ewan-ginger/radian_/Code/Firmware/Waveshare ESP32-S3-LCD-1.85/Arduino/examples/Master/LVGL_Driver.cpp

/*****************************************************************************
  | File        :   LVGL_Driver.c
  
  | help        : 
    The provided LVGL library file must be installed first
******************************************************************************/
#include "LVGL_Driver.h"

static lv_disp_draw_buf_t draw_buf;
static lv_color_t buf1[ LVGL_BUF_LEN ];
static lv_color_t buf2[ LVGL_BUF_LEN];
// static lv_color_t* buf1 = (lv_color_t*) heap_caps_malloc(LVGL_BUF_LEN , MALLOC_CAP_SPIRAM);
// static lv_color_t* buf2 = (lv_color_t*) heap_caps_malloc(LVGL_BUF_LEN , MALLOC_CAP_SPIRAM);
    
/*  Display flushing 
    Displays LVGL content on the LCD
    This function implements associating LVGL data to the LCD screen
*/
void Lvgl_Display_LCD( lv_disp_drv_t *disp_drv, const lv_area_t *area, lv_color_t *color_p )
{
  LCD_addWindow(area->x1, area->y1, area->x2, area->y2, ( uint16_t *)&color_p->full);
  lv_disp_flush_ready( disp_drv );
}
/*Read the touchpad*/
void Lvgl_Touchpad_Read( lv_indev_drv_t * indev_drv, lv_indev_data_t * data )
{
  Simulated_Touch();
  if (touch_data.points != 0x00) {
    data->point.x = touch_data.x;
    data->point.y = touch_data.y;
    data->state = LV_INDEV_STATE_PR;
    // printf("LVGL : X=%u Y=%u points=%d\r\n",  touch_data.x , touch_data.y,touch_data.points);
  } else {
    data->state = LV_INDEV_STATE_REL;
  }
  touch_data.x = 0;
  touch_data.y = 0;
  touch_data.points = 0;
}
void example_increase_lvgl_tick(void *arg)
{
    /* Tell LVGL how many milliseconds has elapsed */
    lv_tick_inc(EXAMPLE_LVGL_TICK_PERIOD_MS);
}
void example_increase_lvgl_Loop_tick(void *arg)
{
  lv_timer_handler(); /* let the GUI do its work */
}
void Lvgl_Init(void)
{
  lv_init();
  lv_disp_draw_buf_init( &draw_buf, buf1, buf2, LVGL_BUF_LEN);

  /*Initialize the display*/
  static lv_disp_drv_t disp_drv;
  lv_disp_drv_init( &disp_drv );
  /*Change the following line to your display resolution*/
  disp_drv.hor_res = LCD_WIDTH;
  disp_drv.ver_res = LCD_HEIGHT;
  disp_drv.flush_cb = Lvgl_Display_LCD;
  disp_drv.full_refresh = 1;                    /**< 1: Always make the whole screen redrawn*/
  disp_drv.draw_buf = &draw_buf;
  lv_disp_drv_register( &disp_drv );

  /*Initialize the (dummy) input device driver*/
  static lv_indev_drv_t indev_drv;
  lv_indev_drv_init( &indev_drv );
  indev_drv.type = LV_INDEV_TYPE_POINTER;
  indev_drv.read_cb = Lvgl_Touchpad_Read;
  lv_indev_drv_register( &indev_drv );


  const esp_timer_create_args_t lvgl_tick_timer_args = {
    .callback = &example_increase_lvgl_tick,
    .name = "lvgl_tick"
  };
  esp_timer_handle_t lvgl_tick_timer = NULL;
  esp_timer_create(&lvgl_tick_timer_args, &lvgl_tick_timer);
  esp_timer_start_periodic(lvgl_tick_timer, EXAMPLE_LVGL_TICK_PERIOD_MS * 1000);

}
void Lvgl_Loop(void)
{
  lv_timer_handler(); /* let the GUI do its work */
}
